ZuluSCSI/ZuluSCSI-Ultra-Wide-OSHW-RP2350B/ZuluSCSI-Ultra-Wide-OSHW.kicad_sch

## KiCad design ZuluSCSI-Ultra-Wide-OSHW.kicad_sch (2026-01-19)

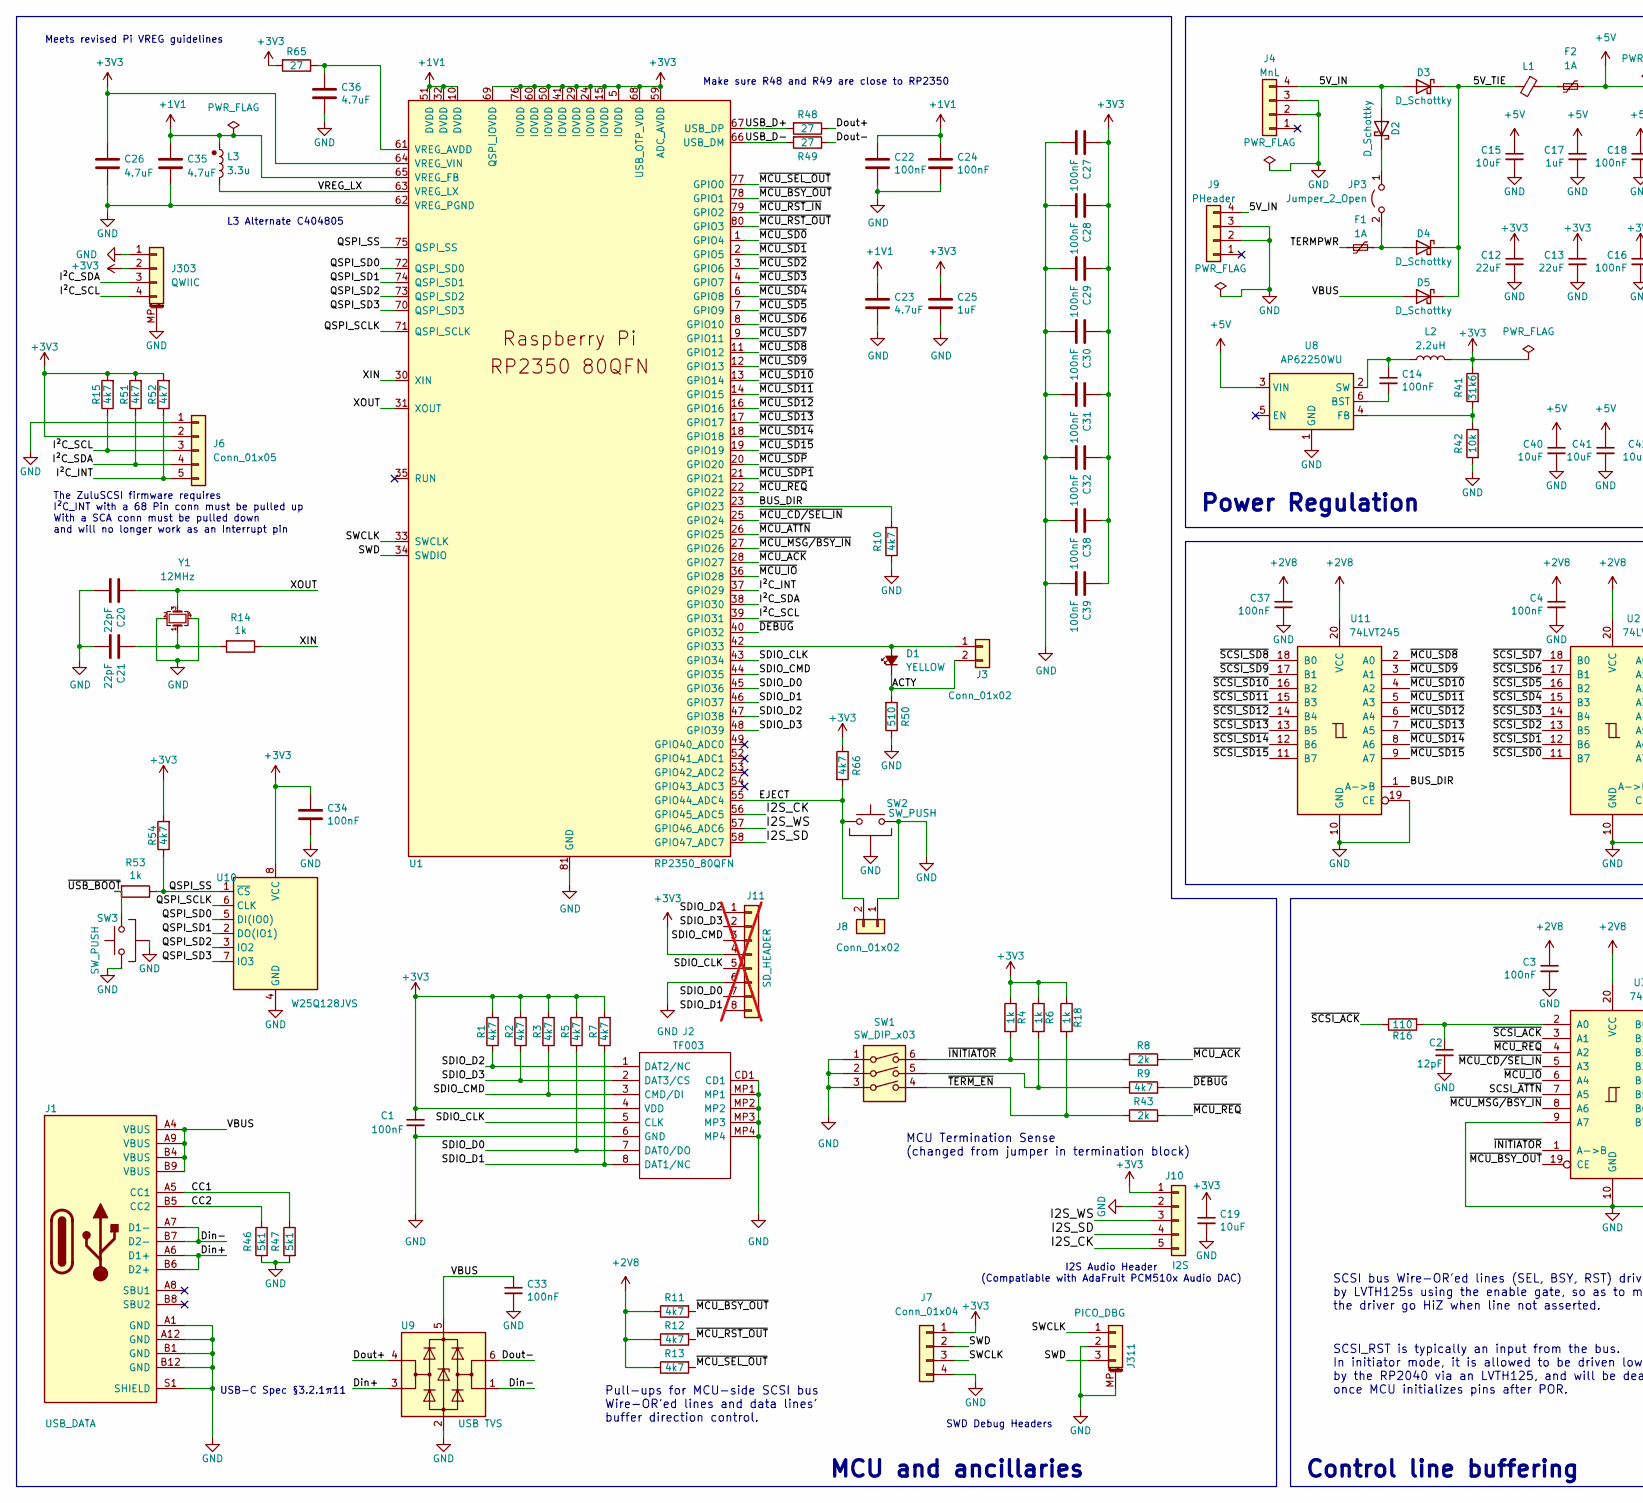
[picture p4: schematic ZuluSCSI-Ultra-Wide-OSHW.kicad_sch, part in row 1, column 1]

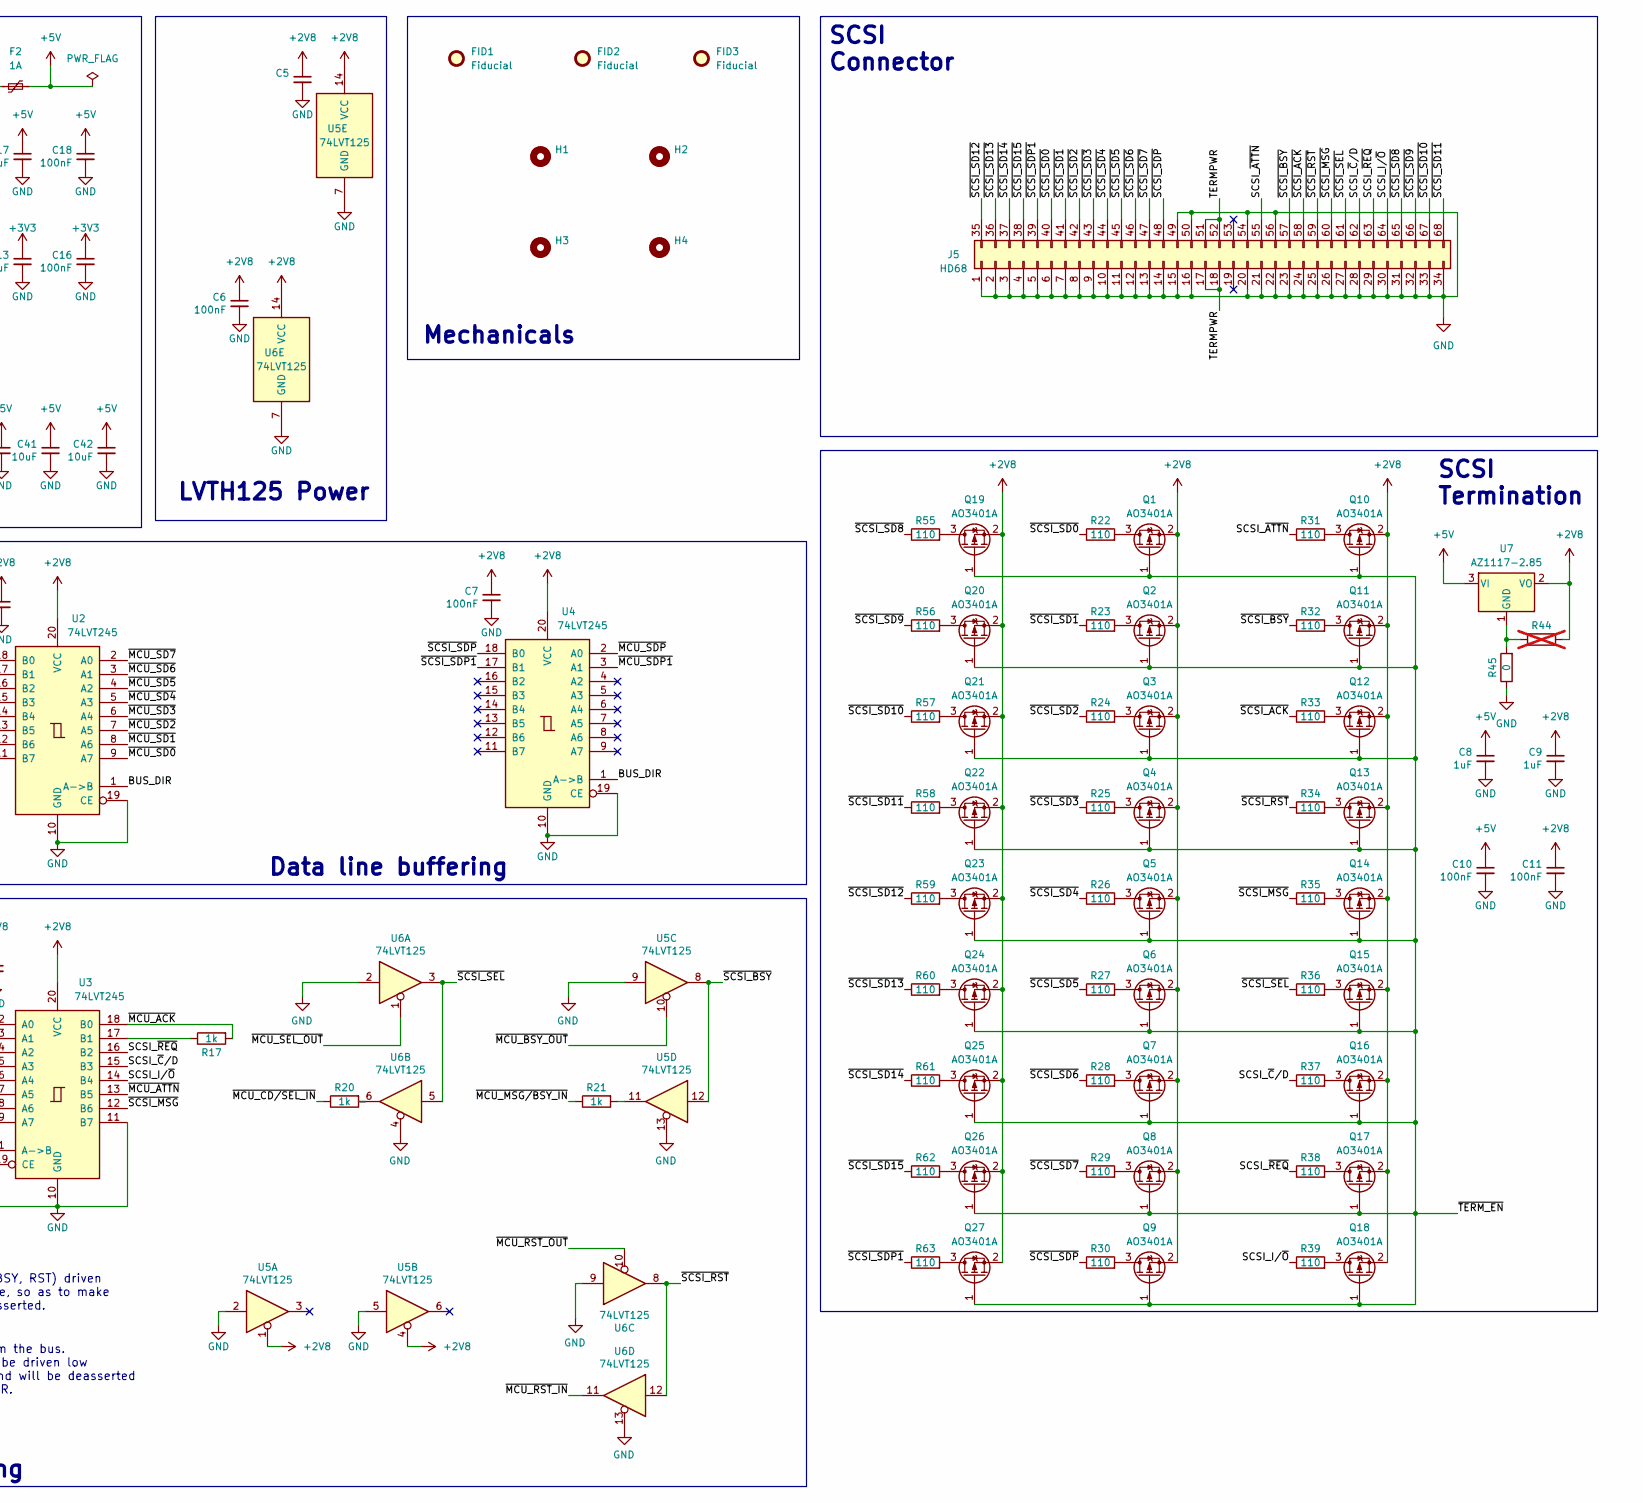
[picture p5: schematic ZuluSCSI-Ultra-Wide-OSHW.kicad_sch, part in row 1, column 2]

Parts:
C1, C3, C4, C5, C6, C7, C10, C11, C14, C16, C18, C37: 100nF; C_0603_1608Metric; LCSC C14663
C2: 12pF; C_0603_1608Metric; LCSC C38523
C8, C9, C17: 1uF; C_0603_1608Metric; LCSC C15849
C12, C13: 22uF; C_0603_1608Metric; LCSC C59461
C15, C19, C40, C41, C42: 10uF; C_0603_1608Metric; LCSC C96446
C20, C21: 22pF; C_0402_1005Metric; LCSC C1555
C22, C24, C27, C28, C29, C30, C31, C32, C33, C34, C38, C39: 100nF; C_0402_1005Metric; LCSC C307331
C23: 4.7uF; C_0402_1005Metric; LCSC C23733
C25: 1uF; C_0402_1005Metric; LCSC C52923
C26, C35: 4.7uF; C_0603_1608Metric; LCSC Part # C19666
C36: 4.7uF; C_0402_1005Metric; LCSC Part # C23733
D1: YELLOW; LED_0603_1608Metric; LCSC C72038
D2, D3, D4, D5: D_Schottky; D_SOD-123; LCSC C82544
F1, F2: 1A; Fuse_0805_2012Metric; LCSC C70061
FID1, FID2, FID3: Fiducial; Fiducial_0.5mm_Mask1mm; LCSC N/A
H1, H2, H3, H4: MH2.5_NPTH; LCSC N/A
J1: USB_DATA; USB_C_Receptacle_HRO_TYPE-C-31-M-12; LCSC C165948
J2: TF003; TF01A; LCSC C5155563
J3, J8: Conn_01x02; PinHeader_1x02_P2.54mm_Vertical; LCSC N/A
J4: MnL; DRVPWR; LCSC N/A
J5: HD68; 5787169-7; LCSC N/A
J6: Conn_01x05; PinHeader_1x05_P2.54mm_Vertical; LCSC N/A
J7: Conn_01x04; PinHeader_1x04_P2.54mm_Vertical; LCSC N/A
J9: PHeader; PinHeader_1x04_P2.54mm_Vertical; LCSC N/A
J10: I2S; PCM510x_1x05_P2.54mm_Vertical
J11: SD_HEADER; PinHeader_1x08_P2.54mm_Vertical; not fitted
J303: QWIIC; JST_SH_BM04B-SRSS-TB_1x04-1MP_P1.00mm_Vertical; LCSC C160390
J311: PICO_DBG; JST_SH_BM03B-SRSS-TB_1x03-1MP_P1.00mm_Vertical; LCSC C160389
JP3: Jumper_2_Open; PinHeader_2x01_P2.54mm_Vertical; LCSC N/A
L1: Ferrite_Bead_Small; L_0603_1608Metric; LCSC C1002
L2: 2.2uH; L_1008_2520Metric_Pad1.43x2.20mm_HandSolder; PartNumber DFE252012P-2R2M=P2; LCSC C86092
L3: 3.3u; L_pol_2016; PartNumber AOTA-B201610S3R3-101-T; digikey 535-AOTA-B201610S3R3-101-TTR-ND
Q1, Q2, Q3, Q4, Q5, Q6, Q7, Q8, Q9, Q10, Q11, Q12, Q13, Q14, Q15, Q16, Q17, Q18, Q19, Q20, Q21, Q22, Q23, Q24, Q25, Q26, Q27: AO3401A; SOT-23; LCSC C15127
R1, R2, R3, R5, R7, R9, R10, R11, R12, R13, R15, R51, R52, R54, R66: 4k7; R_0603_1608Metric; LCSC C23162
R4, R6, R17, R18, R20, R21: 1k; R_0603_1608Metric; LCSC C21190
R8, R43: 2k; R_0603_1608Metric; LCSC C22975
R14, R53: 1k; R_0402_1005Metric; LCSC C11702
R16, R22, R23, R24, R25, R26, R27, R28, R29, R30, R31, R32, R33, R34, R35, R36, R37, R38, R39, R55, R56, R57, R58, R59, R60, R61, R62, R63: 110; R_0603_1608Metric; LCSC C22781
R41: 31k6; R_0603_1608Metric; LCSC C25967
R42: 10k; R_0603_1608Metric; LCSC C25804
R44: R_0603_1608Metric; LCSC N/A; not fitted
R45: 0; R_0603_1608Metric; LCSC C21189
R46, R47: 5k1; R_0402_1005Metric; LCSC C25905
R48, R49, R65: 27; R_0402_1005Metric; LCSC C25092
R50: 510; R_0603_1608Metric; LCSC C23193
SW1: SW_DIP_x03; SW_DIP_SPSTx03_Slide_6.7x9.18mm_W8.61mm_P2.54mm_LowProfile; PartNumber 219-3MSTR; LCSC C319040
SW2, SW3: SW_PUSH; SW-SMD_GT-TC108A-H034-L1S; LCSC C22396279
U1: RP2350_80QFN; RP2350-QFN-80-1EP_10x10_P0.4mm_EP3.4x3.4mm_ThermalVias; LCSC Part # C42415655
U2, U3, U4, U11: 74LVT245; SSOP-20_5.3x7.2mm_P0.65mm; LCSC C74214
U5, U6: 74LVT125; TSSOP-14_4.4x5mm_P0.65mm; LCSC C7042
U7: AZ1117-2.85; SOT-223-3_TabPin2; LCSC C14791
U8: AP62250WU; TSOT-23-6; LCSC C5184228
U9: USB TVS; SOT-23-6; LCSC C2827654
U10: W25Q128JVS; SOIC-8_5.23x5.23mm_P1.27mm; LCSC C97521
Y1: 12MHz; Crystal_SMD_3225-4Pin_3.2x2.5mm; PartNumber ABM8-272-T3; LCSC C20625731

Connections:
5V_IN: D2.2 (A), D3.2 (A), J4.4, J9.4
5V_TIE: D3.1 (K), D4.1 (K), D5.1 (K), L1.2
+1V1: C22.1, C23.1, C24.1, C35.1, L3.1, U1.10 (DVDD), U1.32 (DVDD), U1.51 (DVDD), U1.65 (VREG_FB)
+2V8: C3.1, C4.1, C5.1, C6.1, C7.1, C9.1, C11.1, C37.1, Q1.2 (S), Q2.2 (S), Q3.2 (S), Q4.2 (S), Q5.2 (S), Q6.2 (S), Q7.2 (S), Q8.2 (S), Q9.2 (S), Q10.2 (S), Q11.2 (S), Q12.2 (S), Q13.2 (S), Q14.2 (S), Q15.2 (S), Q16.2 (S), Q17.2 (S), Q18.2 (S), Q19.2 (S), Q20.2 (S), Q21.2 (S), Q22.2 (S), Q23.2 (S), Q24.2 (S), Q25.2 (S), Q26.2 (S), Q27.2 (S), R11.1, R12.1, R13.1, R44.2, U2.20 (VCC), U3.20 (VCC), U4.20 (VCC), U5.1, U5.4, U5.14 (VCC), U6.14 (VCC), U7.2 (VO), U11.20 (VCC)
+3V3: C1.1, C12.1, C13.1, C16.1, C19.1, C25.1, C26.1, C27.1, C28.1, C29.1, C30.1, C31.1, C32.1, C34.1, C38.1, C39.1, J2.4 (VDD), J6.2, J7.1, J10.1, J11.4, J303.2, L2.2, R1.2, R2.2, R3.2, R4.1, R5.2, R6.1, R7.2, R15.2, R18.1, R41.1, R51.2, R52.2, R54.2, R65.2, R66.1, U1.5 (IOVDD), U1.15 (IOVDD), U1.24 (IOVDD), U1.29 (IOVDD), U1.41 (IOVDD), U1.50 (IOVDD), U1.59 (ADC_AVDD), U1.60 (IOVDD), U1.64 (VREG_VIN), U1.68 (USB_OTP_VDD), U1.69 (QSPI_IOVDD), U1.76 (IOVDD), U10.8 (VCC)
+5V: C8.1, C10.1, C15.1, C17.1, C18.1, C40.1, C41.1, C42.1, F2.2, U7.3 (VI), U8.3 (VIN)
ACTY: D1.1 (K), J3.2, R50.2
BUS_DIR: R10.2, U1.23 (GPIO23), U2.1 (A->B), U4.1 (A->B), U11.1 (A->B)
CC1: J1.A5 (CC1), R47.1
CC2: J1.B5 (CC2), R46.1
Din+: J1.A6 (D1+), J1.B6 (D2+), U9.3 (I/O2)
Din-: J1.A7 (D1-), J1.B7 (D2-), U9.1 (I/O1)
Dout+: R48.1, U9.4 (I/O2)
Dout-: R49.1, U9.6 (I/O1)
EJECT: J8.2, R66.2, SW2.2, U1.55 (GPIO44_ADC4)
GND: C1.2, C2.2, C3.2, C4.2, C5.2, C6.2, C7.2, C8.2, C9.2, C10.2, C11.2, C12.2, C13.2, C15.2, C16.2, C17.2, C18.2, C19.2, C20.2, C21.2, C22.2, C23.2, C24.2, C25.2, C26.2, C27.2, C28.2, C29.2, C30.2, C31.2, C32.2, C33.2, C34.2, C35.2, C36.2, C37.2, C38.2, C39.2, C40.2, C41.2, C42.2, J1.A1 (GND), J1.A12 (GND), J1.B1 (GND), J1.B12 (GND), J1.S1 (SHIELD), J2.6 (GND), J2.CD1, J2.MP1, J2.MP2, J2.MP3, J2.MP4, J4.2, J4.3, J5.1, J5.2, J5.3, J5.4, J5.5, J5.6, J5.7, J5.8, J5.9, J5.10, J5.11, J5.12, J5.13, J5.14, J5.15, J5.16, J5.20, J5.21, J5.22, J5.23, J5.24, J5.25, J5.26, J5.27, J5.28, J5.29, J5.30, J5.31, J5.32, J5.33, J5.34, J5.49, J5.50, J5.54, J5.56, J6.1, J7.4, J8.1, J9.2, J9.3, J10.2, J11.6, J303.1, J303.MP (MountPin), J311.2, J311.MP (MountPin), R10.1, R42.2, R45.1, R46.2, R47.2, R50.1, SW1.1, SW1.2, SW1.3, SW2.1, SW2.3 (MNT), SW3.1, SW3.3 (MNT), U1.62 (VREG_PGND), U1.81 (GND), U2.10 (GND), U2.19 (CE), U3.9 (A7), U3.10 (GND), U3.11 (B7), U4.10 (GND), U4.19 (CE), U5.2, U5.5, U5.7 (GND), U5.9, U5.13, U6.2, U6.4, U6.7 (GND), U6.9, U6.13, U8.1 (GND), U9.2 (GND), U10.4 (GND), U11.10 (GND), U11.19 (CE), Y1.2, Y1.4
I2S_CK: J10.5, U1.56 (GPIO45_ADC5)
I2S_SD: J10.4, U1.58 (GPIO47_ADC7)
I2S_WS: J10.3, U1.57 (GPIO46_ADC6)
I²C_INT: J6.5, R52.1, U1.37 (GPIO29)
I²C_SCL: J6.3, J303.4, R15.1, U1.39 (GPIO31)
I²C_SDA: J6.4, J303.3, R51.1, U1.38 (GPIO30)
unnamed: C2.1, R16.2, U3.2 (A0)
unnamed: C14.1, L2.1, U8.2 (SW)
unnamed: C14.2, U8.6 (BST)
unnamed: C21.1, R14.2, Y1.1
unnamed: C36.1, R65.1, U1.61 (VREG_AVDD)
unnamed: D1.2 (A), J3.1, U1.42 (GPIO33)
unnamed: D2.1 (K), JP3.1 (A)
unnamed: D4.2 (A), F1.2, JP3.2 (B)
unnamed: F2.1, L1.1
unnamed: Q1.3 (D), R22.2
unnamed: Q2.3 (D), R23.2
unnamed: Q3.3 (D), R24.2
unnamed: Q4.3 (D), R25.2
unnamed: Q5.3 (D), R26.2
unnamed: Q6.3 (D), R27.2
unnamed: Q7.3 (D), R28.2
unnamed: Q8.3 (D), R29.2
unnamed: Q9.3 (D), R30.2
unnamed: Q10.3 (D), R31.2
unnamed: Q11.3 (D), R32.2
unnamed: Q12.3 (D), R33.2
unnamed: Q13.3 (D), R34.2
unnamed: Q14.3 (D), R35.2
unnamed: Q15.3 (D), R36.2
unnamed: Q16.3 (D), R37.2
unnamed: Q17.3 (D), R38.2
unnamed: Q18.3 (D), R39.2
unnamed: Q19.3 (D), R55.2
unnamed: Q20.3 (D), R56.2
unnamed: Q21.3 (D), R57.2
unnamed: Q22.3 (D), R58.2
unnamed: Q23.3 (D), R59.2
unnamed: Q24.3 (D), R60.2
unnamed: Q25.3 (D), R61.2
unnamed: Q26.3 (D), R62.2
unnamed: Q27.3 (D), R63.2
unnamed: R6.2, R9.1, SW1.5
unnamed: R17.1, U3.17 (B1)
unnamed: R20.2, U6.6
unnamed: R21.2, U5.11
unnamed: R41.2, R42.1, U8.4 (FB)
unnamed: R44.1, R45.2, U7.1 (GND)
QSPI_SCLK: U1.71 (QSPI_SCLK), U10.6 (CLK)
QSPI_SD0: U1.72 (QSPI_SD0), U10.5 (DI(IO0))
QSPI_SD1: U1.74 (QSPI_SD1), U10.2 (DO(IO1))
QSPI_SD2: U1.73 (QSPI_SD2), U10.3 (IO2)
QSPI_SD3: U1.70 (QSPI_SD3), U10.7 (IO3)
QSPI_SS: R53.1, R54.1, U1.75 (QSPI_SS), U10.1 (~CS)
SCSI_I/~O: J5.64, R39.1, U3.14 (B4)
SCSI_~ATTN: J5.55, R31.1, U3.7 (A5)
SCSI_~C/D: J5.62, R37.1, U3.15 (B3)
SCSI_~REQ: J5.63, R38.1, U3.16 (B2)
SDIO_CLK: J2.5 (CLK), J11.5, U1.43 (GPIO34)
SDIO_CMD: J2.3 (CMD/DI), J11.3, R3.1, U1.44 (GPIO35)
SDIO_D0: J2.7 (DAT0/DO), J11.7, R5.1, U1.45 (GPIO36)
SDIO_D1: J2.8 (DAT1/NC), J11.8, R7.1, U1.46 (GPIO37)
SDIO_D2: J2.1 (DAT2/NC), J11.1, R1.1, U1.47 (GPIO38)
SDIO_D3: J2.2 (DAT3/CS), J11.2, R2.1, U1.48 (GPIO39)
SWCLK: J7.3, J311.1, U1.33 (SWCLK)
SWD: J7.2, J311.3, U1.34 (SWDIO)
TERMPWR: F1.1, J5.17, J5.18, J5.51, J5.52
USB_D+: R48.2, U1.67 (USB_DP)
USB_D-: R49.2, U1.66 (USB_DM)
VBUS: C33.1, D5.2 (A), J1.A4 (VBUS), J1.A9 (VBUS), J1.B4 (VBUS), J1.B9 (VBUS), U9.5 (VBUS)
VREG_LX: L3.2, U1.63 (VREG_LX)
XIN: R14.1, U1.30 (XIN)
XOUT: C20.1, U1.31 (XOUT), Y1.3
~DEBUG: R9.2, U1.40 (GPIO32)
~INITIATOR: R4.2, R8.1, SW1.6, U3.1 (A->B)
~MCU_ACK: R8.2, R17.2, U1.28 (GPIO27), U3.18 (B0)
~MCU_ATTN: U1.26 (GPIO25), U3.13 (B5)
~MCU_BSY_OUT: R11.2, U1.78 (GPIO1), U3.19 (CE), U5.10
~MCU_CD/SEL_IN: R20.1, U1.25 (GPIO24), U3.5 (A3)
~MCU_IO: U1.36 (GPIO28), U3.6 (A4)
~MCU_MSG/BSY_IN: R21.1, U1.27 (GPIO26), U3.8 (A6)
~MCU_REQ: R43.2, U1.22 (GPIO22), U3.4 (A2)
~MCU_RST_IN: U1.79 (GPIO2), U6.11
~MCU_RST_OUT: R12.2, U1.80 (GPIO3), U6.10
~MCU_SD0: U1.1 (GPIO4), U2.9 (A7)
~MCU_SD1: U1.2 (GPIO5), U2.8 (A6)
~MCU_SD2: U1.3 (GPIO6), U2.7 (A5)
~MCU_SD3: U1.4 (GPIO7), U2.6 (A4)
~MCU_SD4: U1.6 (GPIO8), U2.5 (A3)
~MCU_SD5: U1.7 (GPIO9), U2.4 (A2)
~MCU_SD6: U1.8 (GPIO10), U2.3 (A1)
~MCU_SD7: U1.9 (GPIO11), U2.2 (A0)
~MCU_SD8: U1.11 (GPIO12), U11.2 (A0)
~MCU_SD9: U1.12 (GPIO13), U11.3 (A1)
~MCU_SD10: U1.13 (GPIO14), U11.4 (A2)
~MCU_SD11: U1.14 (GPIO15), U11.5 (A3)
~MCU_SD12: U1.16 (GPIO16), U11.6 (A4)
~MCU_SD13: U1.17 (GPIO17), U11.7 (A5)
~MCU_SD14: U1.18 (GPIO18), U11.8 (A6)
~MCU_SD15: U1.19 (GPIO19), U11.9 (A7)
~MCU_SDP1: U1.21 (GPIO21), U4.3 (A1)
~MCU_SDP: U1.20 (GPIO20), U4.2 (A0)
~MCU_SEL_OUT: R13.2, U1.77 (GPIO0), U6.1
~SCSI_ACK: J5.58, R16.1, R33.1, U3.3 (A1)
~SCSI_BSY: J5.57, R32.1, U5.8, U5.12
~SCSI_MSG: J5.60, R35.1, U3.12 (B6)
~SCSI_RST: J5.59, R34.1, U6.8, U6.12
~SCSI_SD0: J5.40, R22.1, U2.11 (B7)
~SCSI_SD1: J5.41, R23.1, U2.12 (B6)
~SCSI_SD2: J5.42, R24.1, U2.13 (B5)
~SCSI_SD3: J5.43, R25.1, U2.14 (B4)
~SCSI_SD4: J5.44, R26.1, U2.15 (B3)
~SCSI_SD5: J5.45, R27.1, U2.16 (B2)
~SCSI_SD6: J5.46, R28.1, U2.17 (B1)
~SCSI_SD7: J5.47, R29.1, U2.18 (B0)
~SCSI_SD8: J5.65, R55.1, U11.18 (B0)
~SCSI_SD9: J5.66, R56.1, U11.17 (B1)
~SCSI_SD10: J5.67, R57.1, U11.16 (B2)
~SCSI_SD11: J5.68, R58.1, U11.15 (B3)
~SCSI_SD12: J5.35, R59.1, U11.14 (B4)
~SCSI_SD13: J5.36, R60.1, U11.13 (B5)
~SCSI_SD14: J5.37, R61.1, U11.12 (B6)
~SCSI_SD15: J5.38, R62.1, U11.11 (B7)
~SCSI_SDP1: J5.39, R63.1, U4.17 (B1)
~SCSI_SDP: J5.48, R30.1, U4.18 (B0)
~SCSI_SEL: J5.61, R36.1, U6.3, U6.5
~TERM_EN: Q1.1 (G), Q2.1 (G), Q3.1 (G), Q4.1 (G), Q5.1 (G), Q6.1 (G), Q7.1 (G), Q8.1 (G), Q9.1 (G), Q10.1 (G), Q11.1 (G), Q12.1 (G), Q13.1 (G), Q14.1 (G), Q15.1 (G), Q16.1 (G), Q17.1 (G), Q18.1 (G), Q19.1 (G), Q20.1 (G), Q21.1 (G), Q22.1 (G), Q23.1 (G), Q24.1 (G), Q25.1 (G), Q26.1 (G), Q27.1 (G), R18.2, R43.1, SW1.4
~USB_BOOT: R53.2, SW3.2

Notes on the sheet:
Pull-ups for MCU-side SCSI bus Wire-OR'ed lines and data lines' buffer direction control.
Meets revised Pi VREG guidelines
MCU and ancillaries
SCSI_RST is typically an input from the bus. In initiator mode, it is allowed to be driven low by the RP2040 via an LVTH125, and will be deasserted once MCU initializes pins after POR.
Data line buffering
LVTH125 Power
I2S Audio Header (Compatiable with AdaFruit PCM510x Audio DAC)
Power Regulation
SCSI Connector
L3 Alternate C404805
The ZuluSCSI firmware requires I²C_INT with a 68 Pin conn must be pulled up With a SCA conn must be pulled down and will no longer work as an Interrupt pin
USB-C Spec §3.2.1¶11
Mechanicals
SWD Debug Headers
MCU Termination Sense (changed from jumper in termination block)
Control line buffering
SCSI bus Wire-OR'ed lines (SEL, BSY, RST) driven by LVTH125s using the enable gate, so as to make the driver go HiZ when line not asserted.
Make sure R48 and R49 are close to RP2350
SCSI Termination
